RetroStack/TRS-80-Model-I-Keyboard-MX/Images/Bezel_Back.png

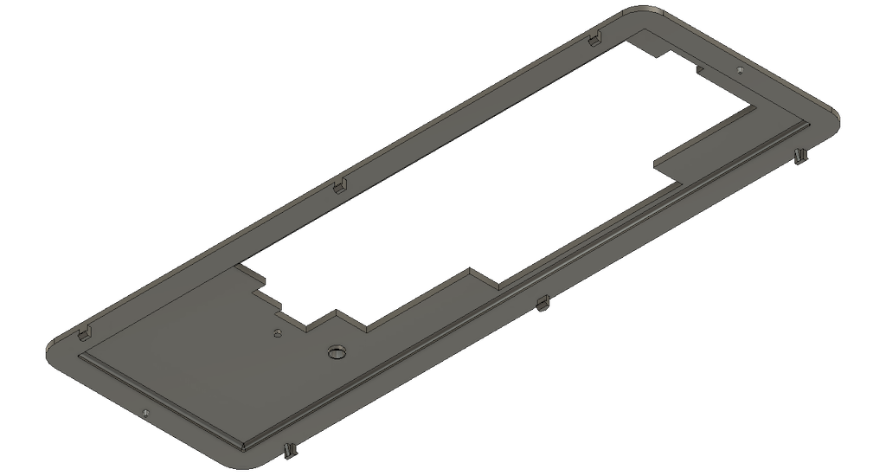
Images/Bezel_Back.png
