RetroStack/TRS-80-Model-I-Keyboard-MX/Images/Bezel_Front.png

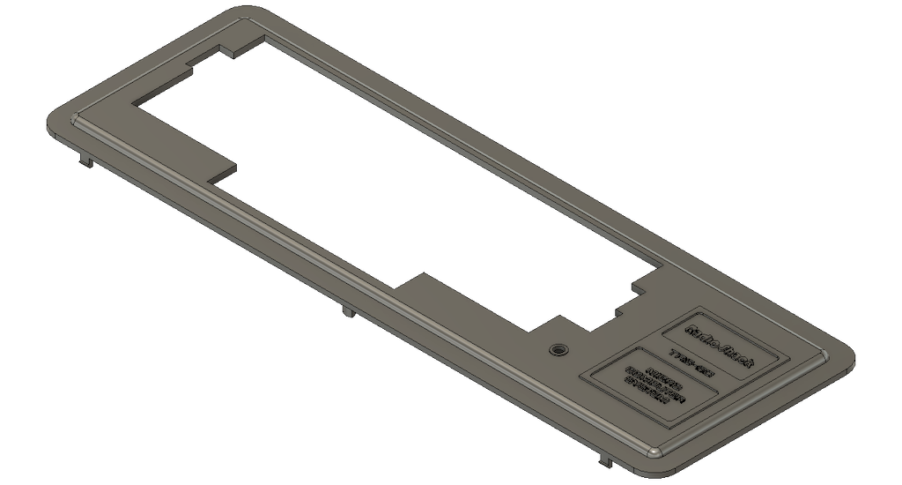
Images/Bezel_Front.png
