RetroStack/TRS-80-Model-I-Keyboard-MX/Images/LED_StandOff.png

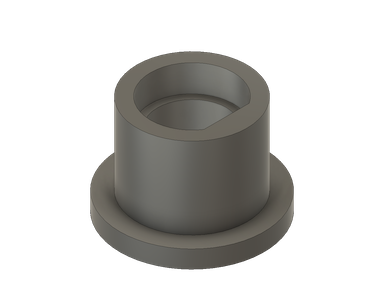
Images/LED_StandOff.png
