RetroStack/TRS-80-Model-I-Keyboard-MX/Images/Shield_Flat_Pattern.png

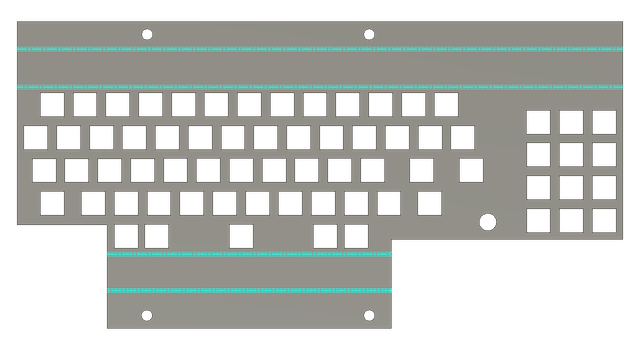
Images/Shield_Flat_Pattern.png
